T3chy/ditaqm/boards/esp8266/firmware/ap.py

import machine
from machine import Pin, I2C
import time
import re
import json
import ssd1306

try:
    i2c = machine.I2C(-1, machine.Pin(5), machine.Pin(4)) # this(-1) may not work on ESP32
    oled = ssd1306.SSD1306_I2C(128, 32, i2c)
    is_oled = True
    oled.fill(0)
    oled.text("booting",0,0)
    oled.show()
except Exception as e:
    print(e)
    is_oled = False


def say(msg, snd=0): # maybe useful if it can handle multiple lines (array input?)
    if is_oled:
        oled.fill(0)
        oled.text(str(msg), 0,0)
        if snd:
            oled.text(str(snd), 0, 10)
        oled.show()
    print(msg)
    print(snd if snd else "")
# ************************
# Configure the ESP32 wifi
# as Access Point mode.
import network

sta = network.WLAN(network.STA_IF)
sta.active(True)
say("enabling STA..")
while not sta.active():
    pass




# ************************
# Configure the socket connection
# over TCP/IP
import socket


# ************************
# Functions for creating the
# web pages to be displayed
def web_page():
    html_page = """<!DOCTYPE HTML>
        <html>
        <head>
          <meta name="viewport" content="width=device-width, initial-scale=1">
        </head>
        <body>
           <center><h2>Welcome to your Air Quality Cluster!</h2></center>
           <center><h2>Please Select a SSID and enter a password to connect to a network!</h2></center>
           <center>
             <form>
                """ + scanstr + """
               <input id='pass' type='text' name="pass" placeholder="pass">
               <input type="submit" value="Submit">
             </form>
           </center>
           </body>
        </html>"""
    return html_page
def success():
    html_page = """<!DOCTYPE HTML>
        <html>
        <head>
          <meta name="viewport" content="width=device-width, initial-scale=1">
        </head>
        <body>
           <center><h2>Success! the device will now reboot. Connect (on the device you want to access the cluster from) to the wifi network you just entered the credentials for, and follow the instructions on the OLED!</h2></center>
           <center>
           </center>
           </body>
        </html>"""
    return html_page

flag = 0
def finish(conn):
    print("connected! " + str(sta.ifconfig()))
    response = success()
    conn.send('HTTP/1.1 200 OK\n')
    conn.send('Content-Type: text/html\n')
    conn.send('Connection: close\n\n')
    conn.sendall(response)
    conn.close()
    time.sleep(1)
    ap.active(False)

try:
    with open("config.json", "r") as f:
        try:
            data = json.load(f)
            sta.connect(str(data["ssid"]), str(data["passwd"]))
            counter = 0
            while not sta.isconnected():
                time.sleep(1)
                counter += 1
                if counter > 5:
                    break
            if sta.isconnected():
                flag = 1
        except Exception as e:
            print(e)
except:
    pass

if not flag:
    ap_ssid = 'Your Air Quality Cluster!'
    ap_passwd = '12345678'
    say("scanning SSIDs...")
    scan = [net[0] for net in sta.scan()]

    say("enabling AP...")
    ap = network.WLAN(network.AP_IF)
    ap.active(True)
    ap.config(essid=ap_ssid, password=ap_passwd)
    while not ap.active():
        pass
    print('network config:', ap.ifconfig())
    scanstr = "<select id=\"ssid\" name=\"ssid\">"
    for ssid in scan:
        ssid = str(ssid).strip('b').strip('\'').strip("\"")
        scanstr = scanstr + "<option value= \"" + ssid + "\">" + ssid + "</option>"
    scanstr = scanstr + "</select>"
    say("AP Enabled!")
    time.sleep(1)
    say("SSID:" + ap_ssid, snd="pass:" + ap_passwd)
    time.sleep(5)
    # AF_INET - use Internet Protocol v4 addresses
    # SOCK_STREAM means that it is a TCP socket.
    # SOCK_DGRAM means that it is a UDP socket.
    s = socket.socket(socket.AF_INET, socket.SOCK_STREAM)
    s.bind(('',80)) # specifies that the socket is reachable by any address the machine happens to have
    s.listen(5)     # max of 5 socket connections
    print('serving')
    while True:
        say("http://" + str(ap.ifconfig()[0]))
        conn, addr = s.accept()
        request=conn.recv(1024)
        # print("Content %s" % str(request))
        ssid = None
        passwd = None
        request = str(request, 'utf8')
        if sta.isconnected():
            finish(conn)
            break
        if "GET /?ssid=" in request:
            print('ssid request time')
            try:
                ssid = re.search(r"ssid=(.*?)\&", request).group(1).strip()
                passwd = re.search(r"pass=(.*?)\ HTTP", request).group(1).strip()
                if ssid and passwd:
                    print("ssid:", ssid)
                    print("pass:", passwd)
                    sta.connect(str(ssid), str(passwd))
                    counter = 0
                    while not sta.isconnected():
                        time.sleep(1)
                        counter += 1
                        if counter > 5:
                            break
                    finish(conn)
                    break
            except Exception as e:
                print(e)

        # Socket send()
        response = web_page()
        conn.send('HTTP/1.1 200 OK\n')
        conn.send('Content-Type: text/html\n')
        conn.send('Connection: close\n\n')
        conn.sendall(response)
        conn.close()
    with open("config.json", "w") as f:
        try:
            data = json.load(f)
        except:
            data = {}
        data["ssid"] = ssid
        data["passwd"] = passwd
        json.dump(data, f)
        say("Config stored,", snd="connected to WLAN!")
        machine.reset()
else:
    say("connected to WLAN!")
